TGit-Tech/DIN-Rail-3D-Printer/3D-Prints-STL/Footing-FlipR.stl

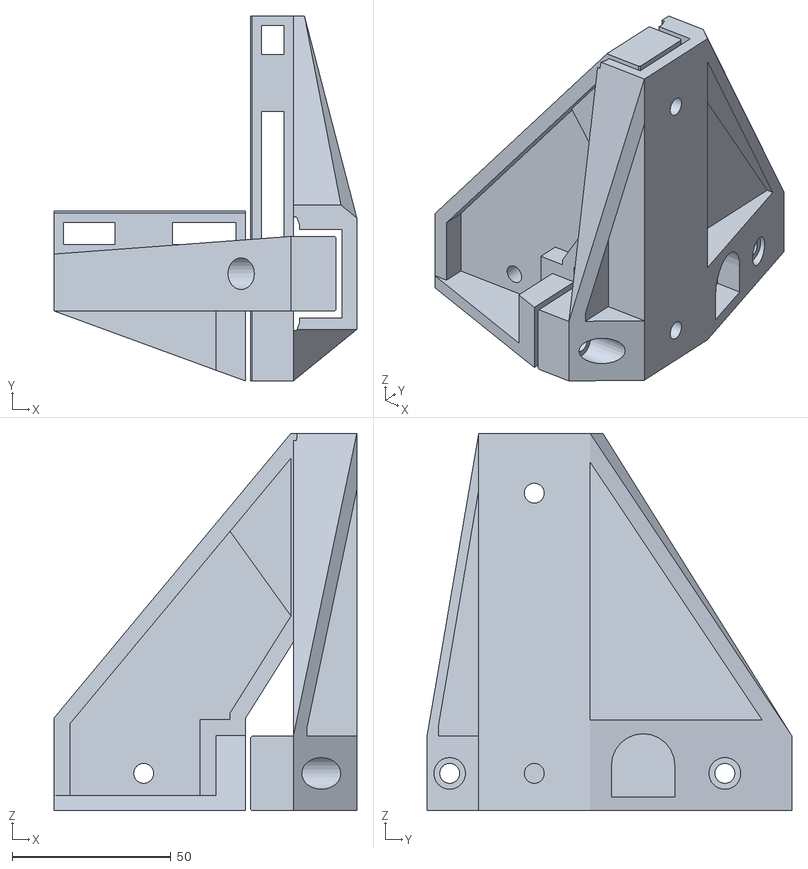
[picture p18: CAD file, 2018-04-14]
3D-Prints-STL/Footing-FlipR.stl
95.4 x 115.0 x 118.9
