TGit-Tech/DIN-Rail-3D-Printer/3D-Prints-STL/Z-Endstop-Base.stl

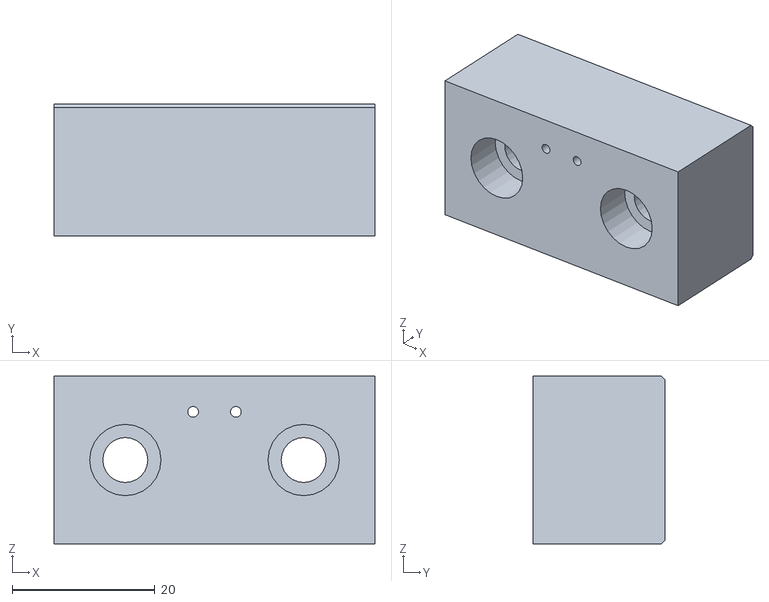
[picture p19: CAD file, 2018-04-14]
3D-Prints-STL/Z-Endstop-Base.stl
45.0 x 18.5 x 23.5
