TGit-Tech/DIN-Rail-3D-Printer/3D-Prints-STL/Z-Endstop-Bracket.stl

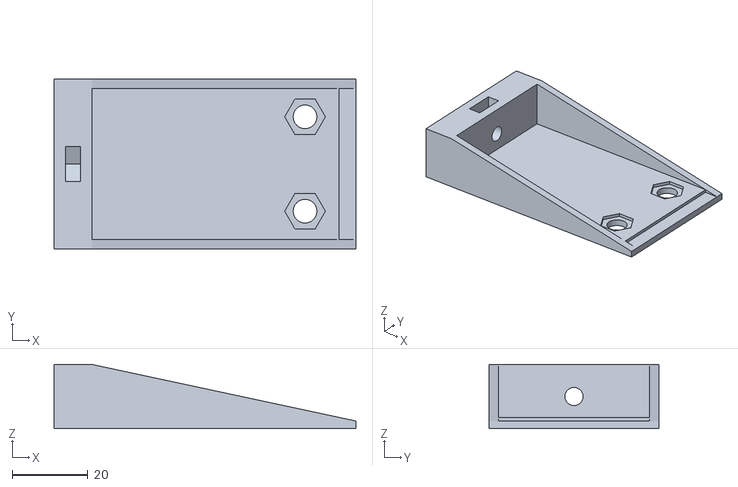
[picture p20: CAD file, 2018-04-14]
3D-Prints-STL/Z-Endstop-Bracket.stl
80.0 x 45.0 x 17.0
