TGit-Tech/DIN-Rail-3D-Printer/3D-Prints-STL/Gantry-Corner-FL-YPulley-FlipG.stl

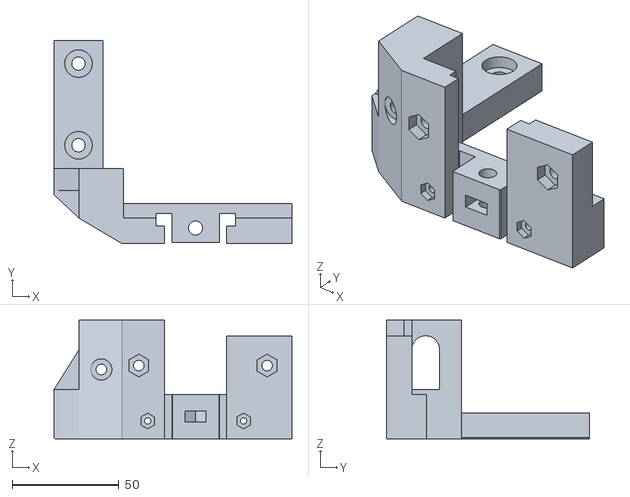
[picture p21: CAD file, 2018-03-04]
3D-Prints-STL/Gantry-Corner-FL-YPulley-FlipG.stl
111.7 x 95.2 x 55.6
