TGit-Tech/DIN-Rail-3D-Printer/3D-Prints-STL/Top-Corner-Flipped.stl

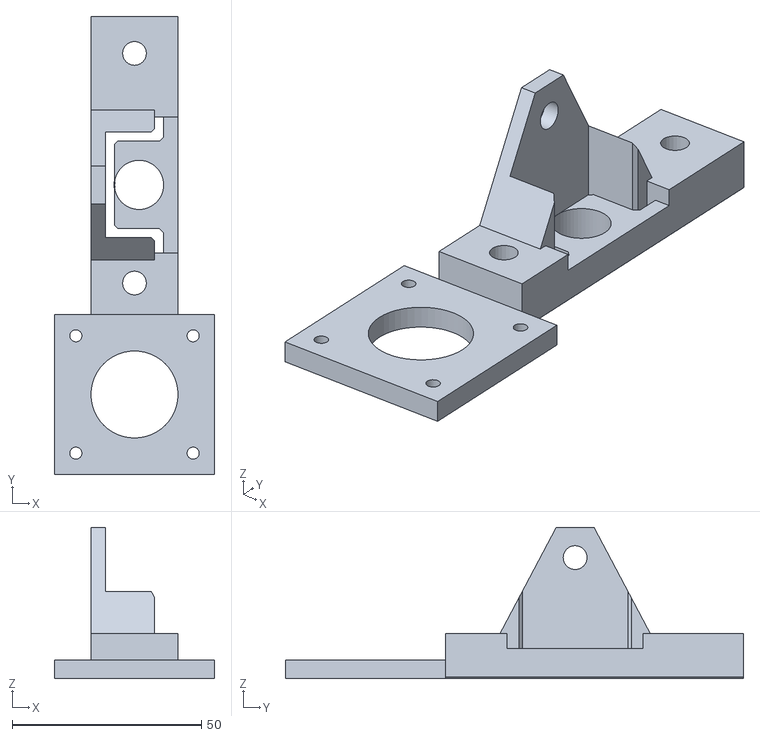
[picture p22: CAD file, 2018-03-04]
3D-Prints-STL/Top-Corner-Flipped.stl
42.3 x 121.1 x 40.0
