TGit-Tech/DIN-Rail-3D-Printer/3D-Prints-STL/Gantry-Corner-BL-YMotor-FlipR.stl

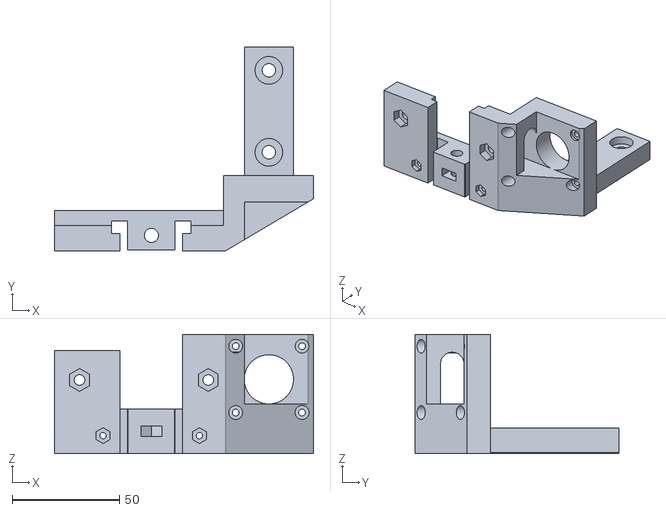
[picture p23: CAD file, 2018-03-04]
3D-Prints-STL/Gantry-Corner-BL-YMotor-FlipR.stl
121.0 x 95.2 x 55.6
