TGit-Tech/DIN-Rail-3D-Printer/3D-Prints-STL/Top-ThreadedRodGear.stl

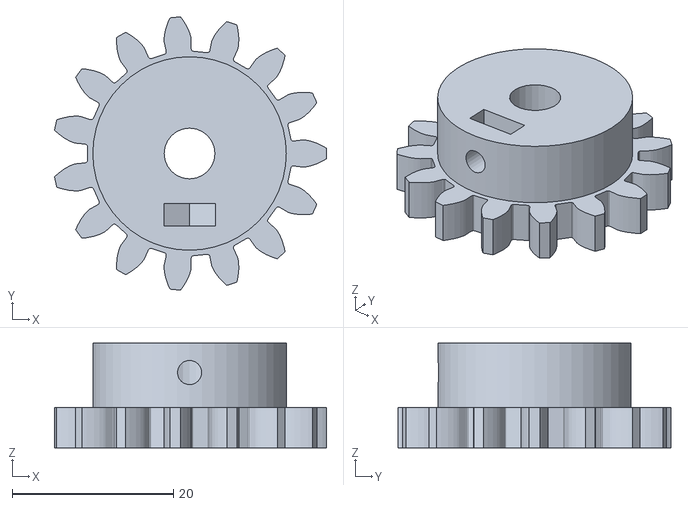
[picture p24: CAD file, 2018-03-04]
3D-Prints-STL/Top-ThreadedRodGear.stl
33.7 x 33.9 x 13.0
