TGit-Tech/DIN-Rail-3D-Printer/3D-Prints-STL/X-Motor-Bracket.stl

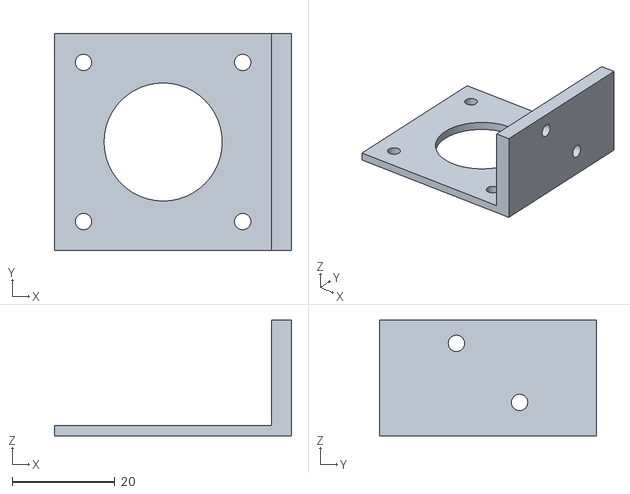
[picture p25: CAD file, 2018-03-04]
3D-Prints-STL/X-Motor-Bracket.stl
46.2 x 42.3 x 22.5
