TGit-Tech/DIN-Rail-3D-Printer/3D-Prints-STL/Top-Center-Rail-End.stl

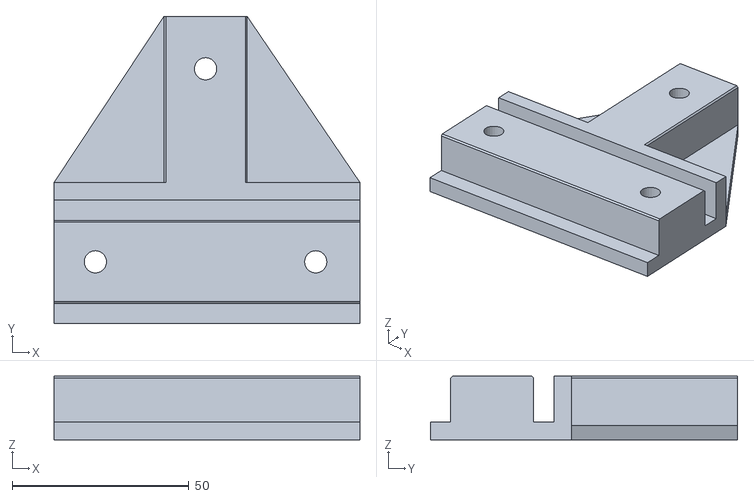
[picture p26: CAD file, 2018-03-04]
3D-Prints-STL/Top-Center-Rail-End.stl
86.5 x 86.9 x 18.0
