TGit-Tech/DIN-Rail-3D-Printer/3D-Prints-STL/Top-Motor-Gear.stl

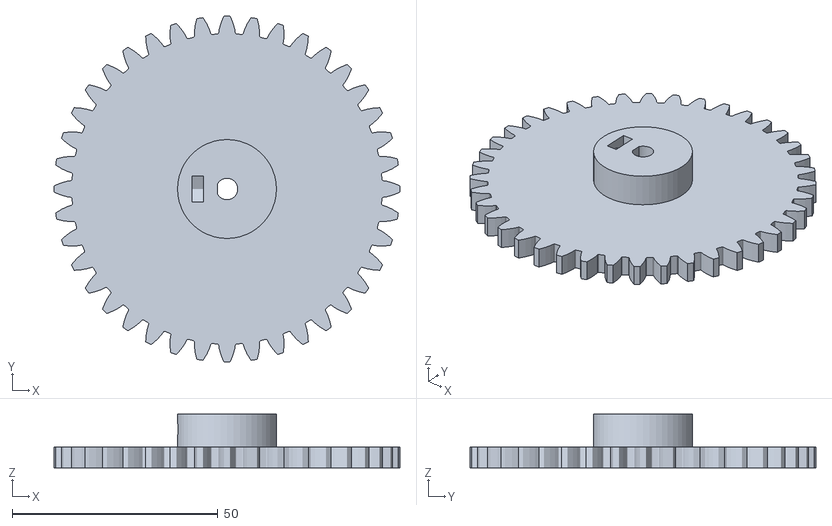
[picture p27: CAD file, 2018-03-04]
3D-Prints-STL/Top-Motor-Gear.stl
84.0 x 84.0 x 13.0
