TGit-Tech/DIN-Rail-3D-Printer/3D-Prints-STL/Y-Carriage.stl

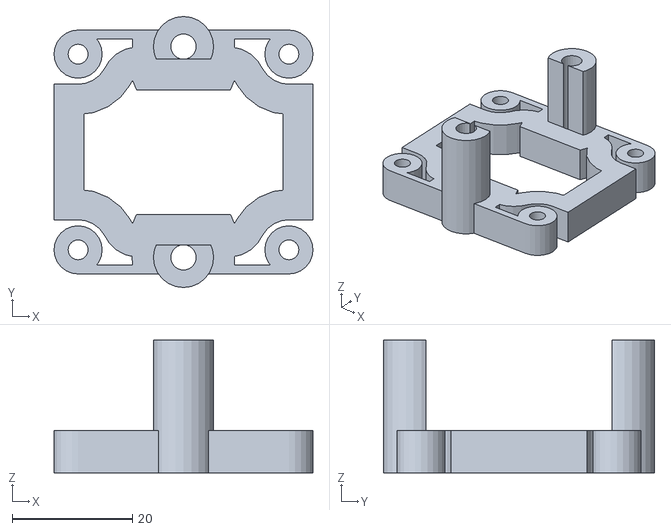
[picture p28: CAD file, 2018-03-04]
3D-Prints-STL/Y-Carriage.stl
43.0 x 45.0 x 22.0
