TGit-Tech/DIN-Rail-3D-Printer/3D-Prints-JPG/Extruder-Head.png

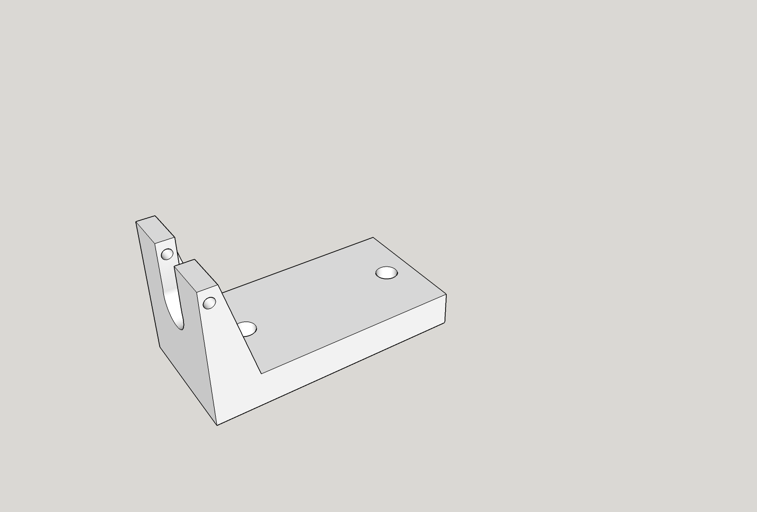
3D-Prints-JPG/Extruder-Head.png
