TGit-Tech/DIN-Rail-3D-Printer/3D-Prints-JPG/Footing.png

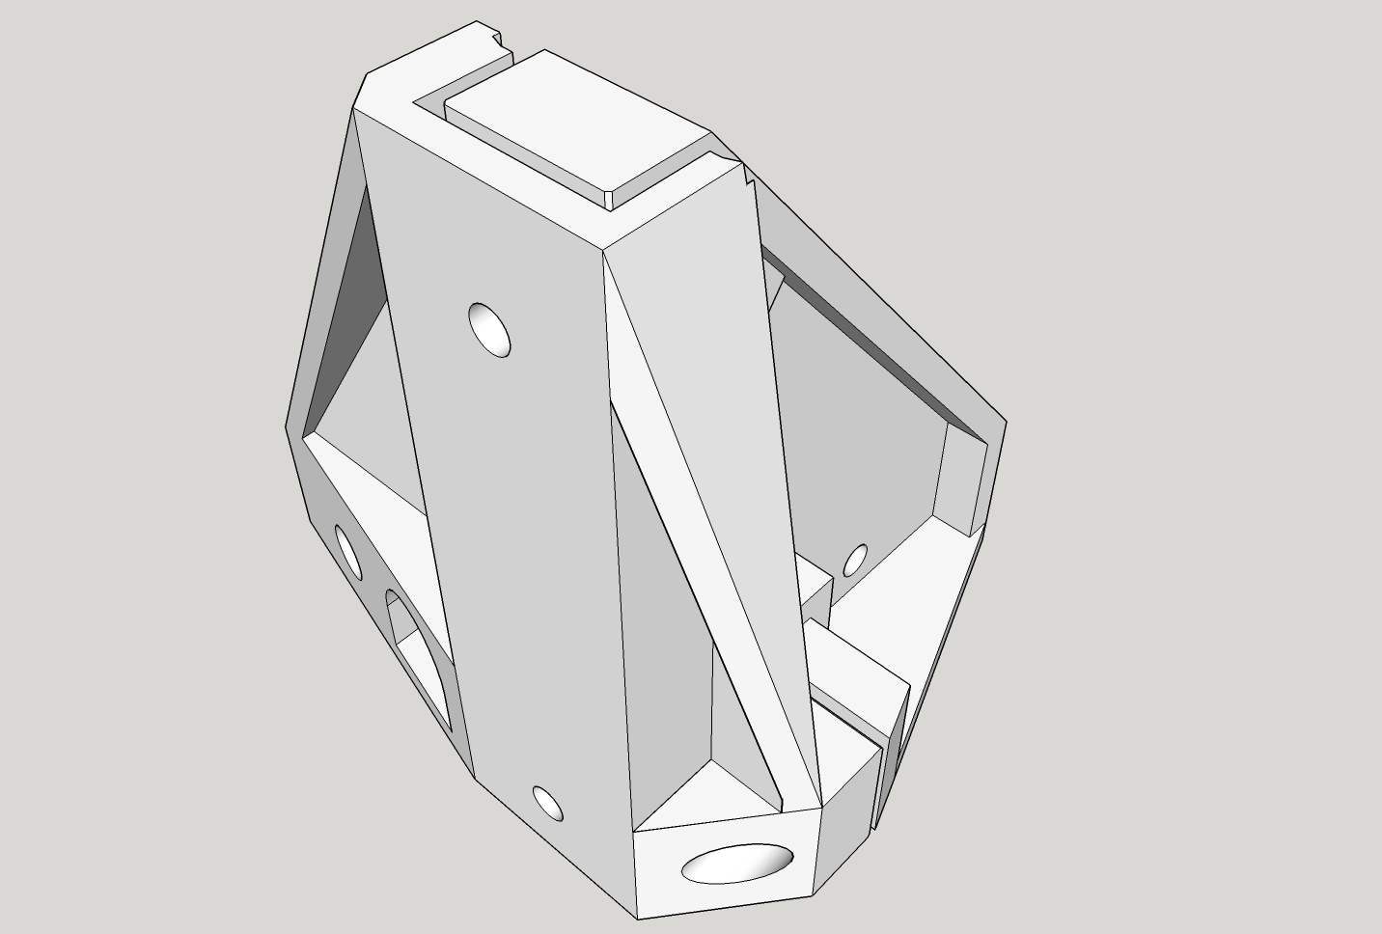
3D-Prints-JPG/Footing.png
