TGit-Tech/DIN-Rail-3D-Printer/3D-Prints-JPG/Gantry-Corner-YPulley-Flipped.png

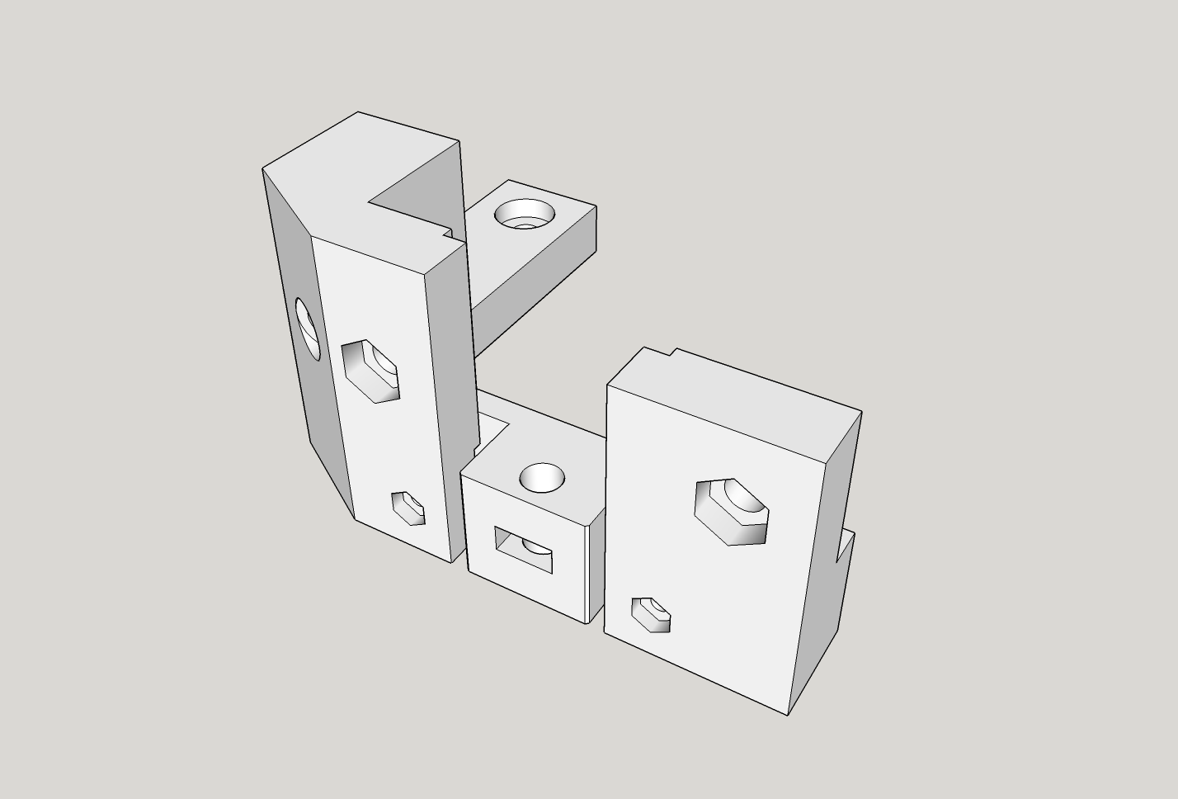
3D-Prints-JPG/Gantry-Corner-YPulley-Flipped.png
