TGit-Tech/DIN-Rail-3D-Printer/3D-Prints-JPG/Top-Corner.png

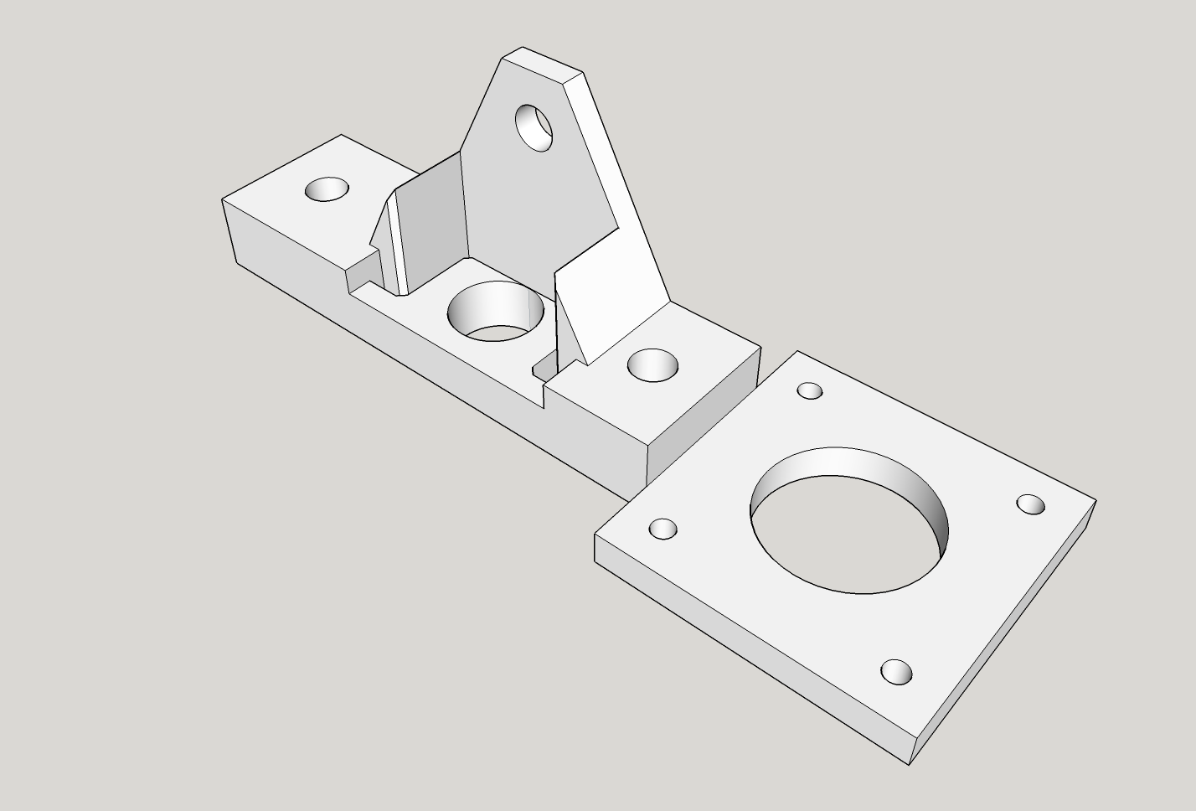
3D-Prints-JPG/Top-Corner.png
