TGit-Tech/DIN-Rail-3D-Printer/3D-Prints-JPG/X-Gantry-End.png

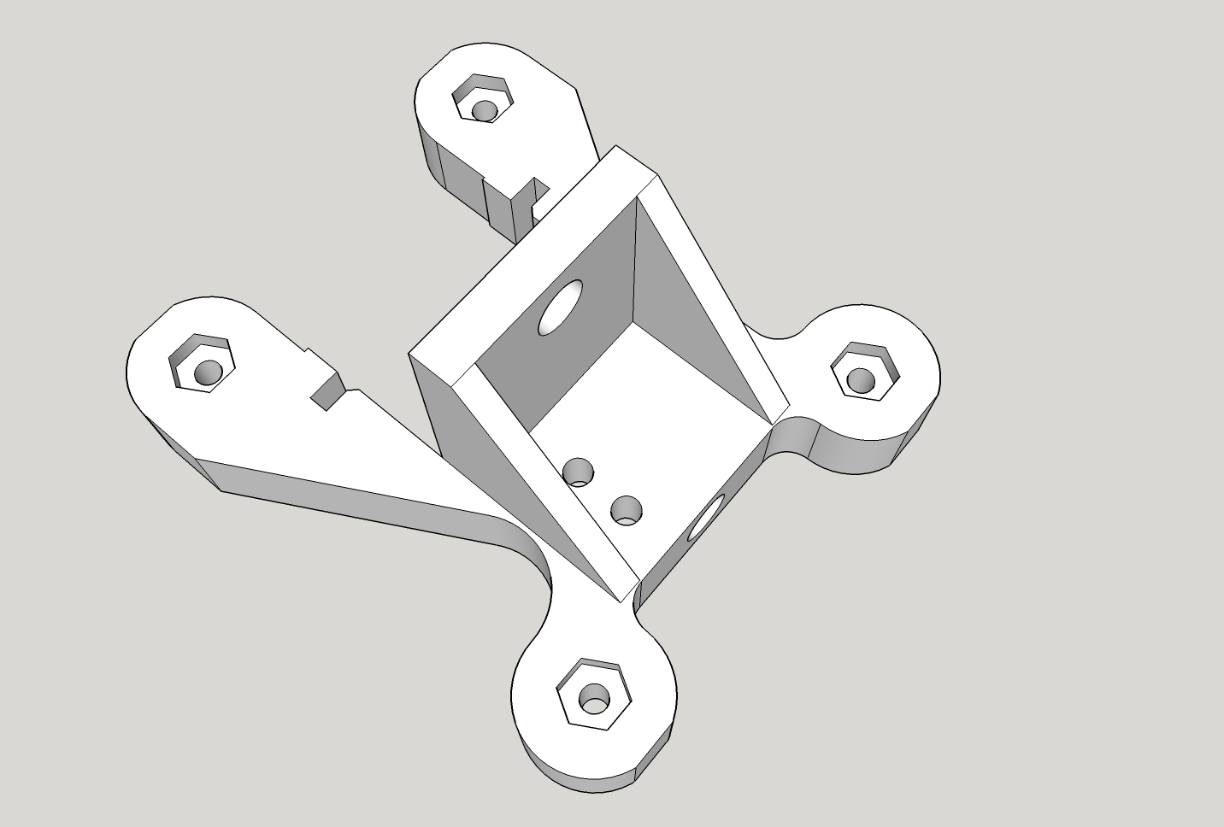
3D-Prints-JPG/X-Gantry-End.png
